SILICPY/Mjoelnir/hardware/cad/drawings/in/verschluss.dxf

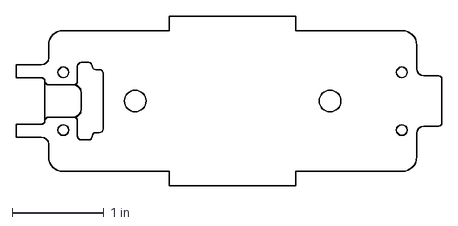
[picture p18: CAD file, 2025-05-09]
hardware/cad/drawings/in/verschluss.dxf
4.65 x 1.85 in
