SILICPY/Mjoelnir/hardware/cad/drawings/in/kappe_rechts_1.dxf

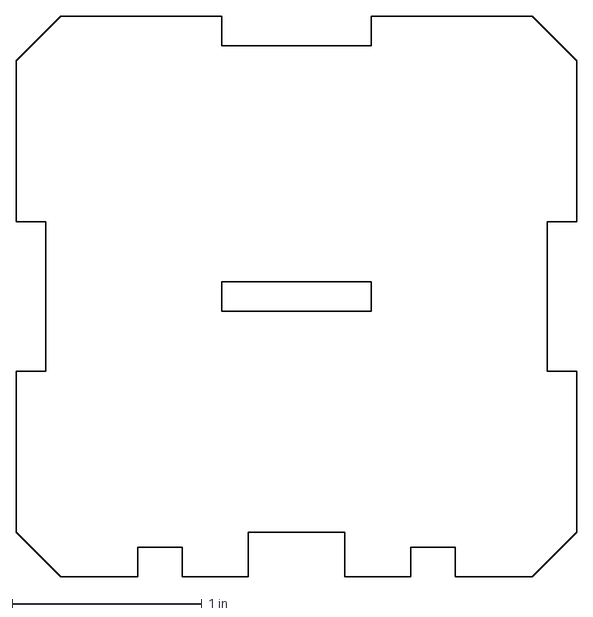
[picture p19: CAD file, 2025-05-09]
hardware/cad/drawings/in/kappe_rechts_1.dxf
2.95 x 2.95 in
