SILICPY/Mjoelnir/hardware/cad/drawings/in/wand_unten.dxf

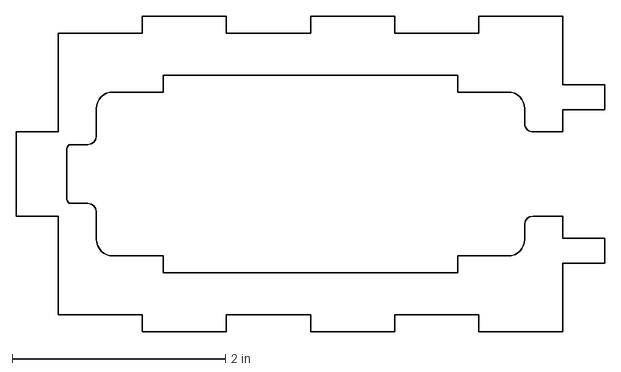
[picture p20: CAD file, 2025-05-09]
hardware/cad/drawings/in/wand_unten.dxf
5.51 x 2.95 in
