SILICPY/Mjoelnir/hardware/cad/drawings/in/led_befestigung_vorne.dxf

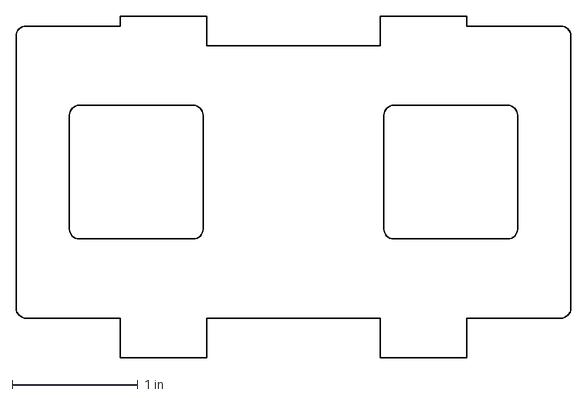
[picture p21: CAD file, 2025-05-09]
hardware/cad/drawings/in/led_befestigung_vorne.dxf
4.41 x 2.72 in
