SILICPY/Mjoelnir/hardware/cad/drawings/in/wand_vorne.dxf

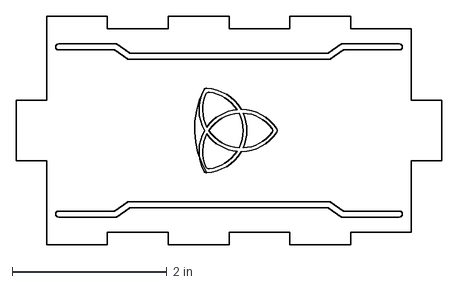
[picture p22: CAD file, 2025-05-09]
hardware/cad/drawings/in/wand_vorne.dxf
5.51 x 2.95 in
